stefan-lochbrunner/Pro-Trinket-USB-Keyboard/hw/Pro Trinket-Micro Keyboard Jr/hw/Pro Trinket-Micro Keyboard Jr v1.brd.png

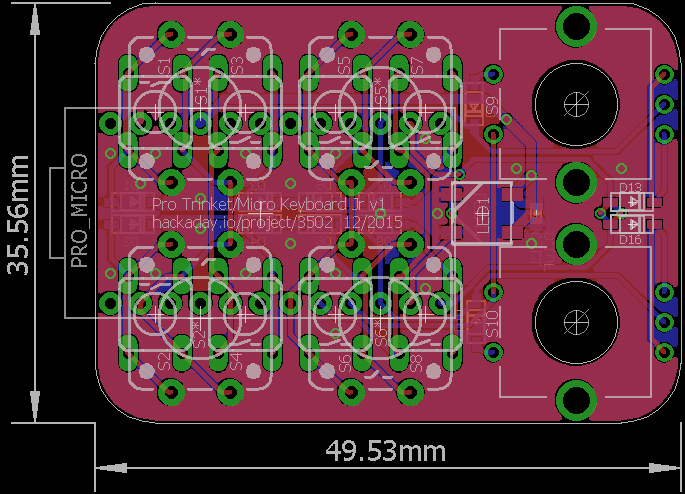
hw/Pro Trinket-Micro Keyboard Jr/hw/Pro Trinket-Micro Keyboard Jr v1.brd.png
