stefan-lochbrunner/Pro-Trinket-USB-Keyboard/Pro Trinket Keyboard/hw/schematics/Pro Trinket Keyboard V1.png

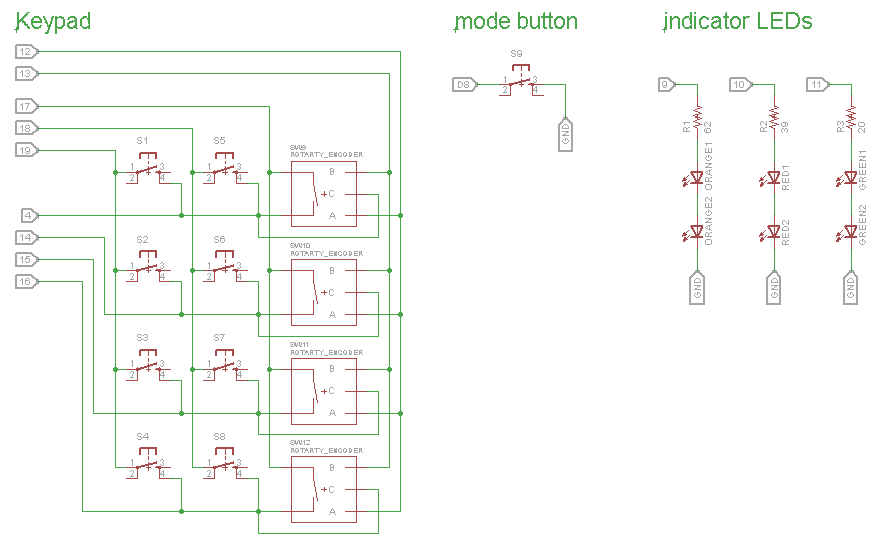
Pro Trinket Keyboard/hw/schematics/Pro Trinket Keyboard V1.png
