stefan-lochbrunner/Pro-Trinket-USB-Keyboard/Pro Trinket Keyboard/hw/schematics/Pro Trinket Keyboard V3.1.sch.png

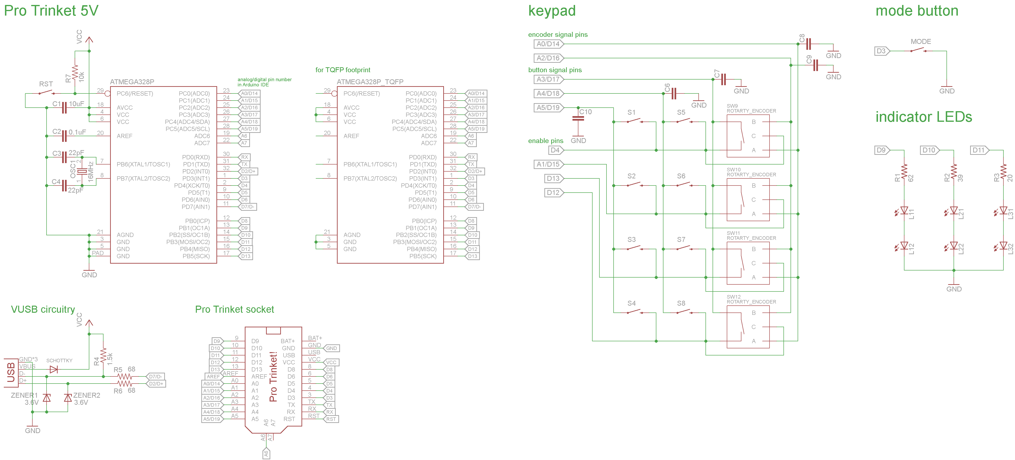
Pro Trinket Keyboard/hw/schematics/Pro Trinket Keyboard V3.1.sch.png
