stefan-lochbrunner/Pro-Trinket-USB-Keyboard/Pro Trinket Keyboard/hw/schematics/Pro Trinket Keyboard V3.3.brd.png

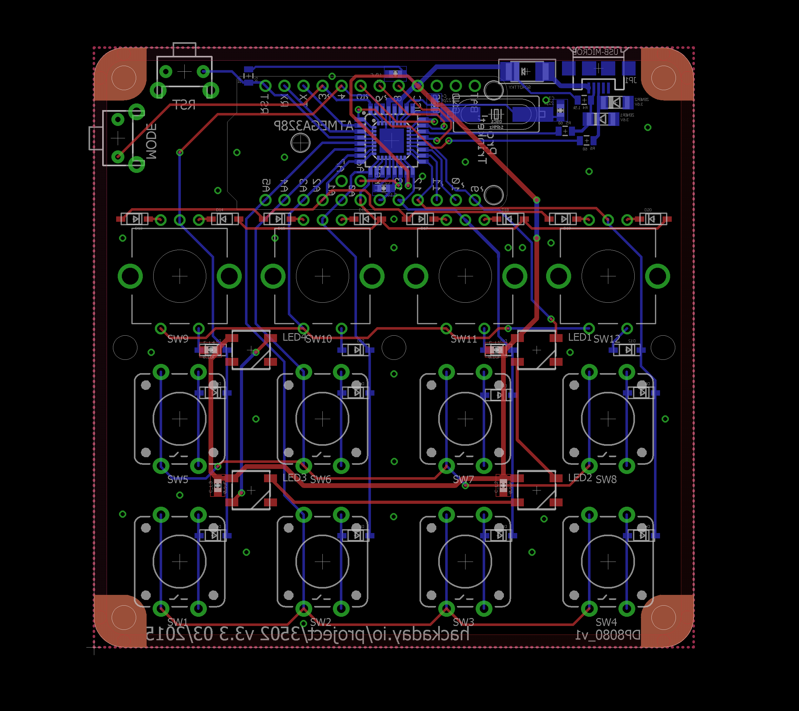
Pro Trinket Keyboard/hw/schematics/Pro Trinket Keyboard V3.3.brd.png
