stefan-lochbrunner/Pro-Trinket-USB-Keyboard/Pro Trinket Keyboard/hw/schematics/Pro Trinket Keyboard V4.2.brd.png

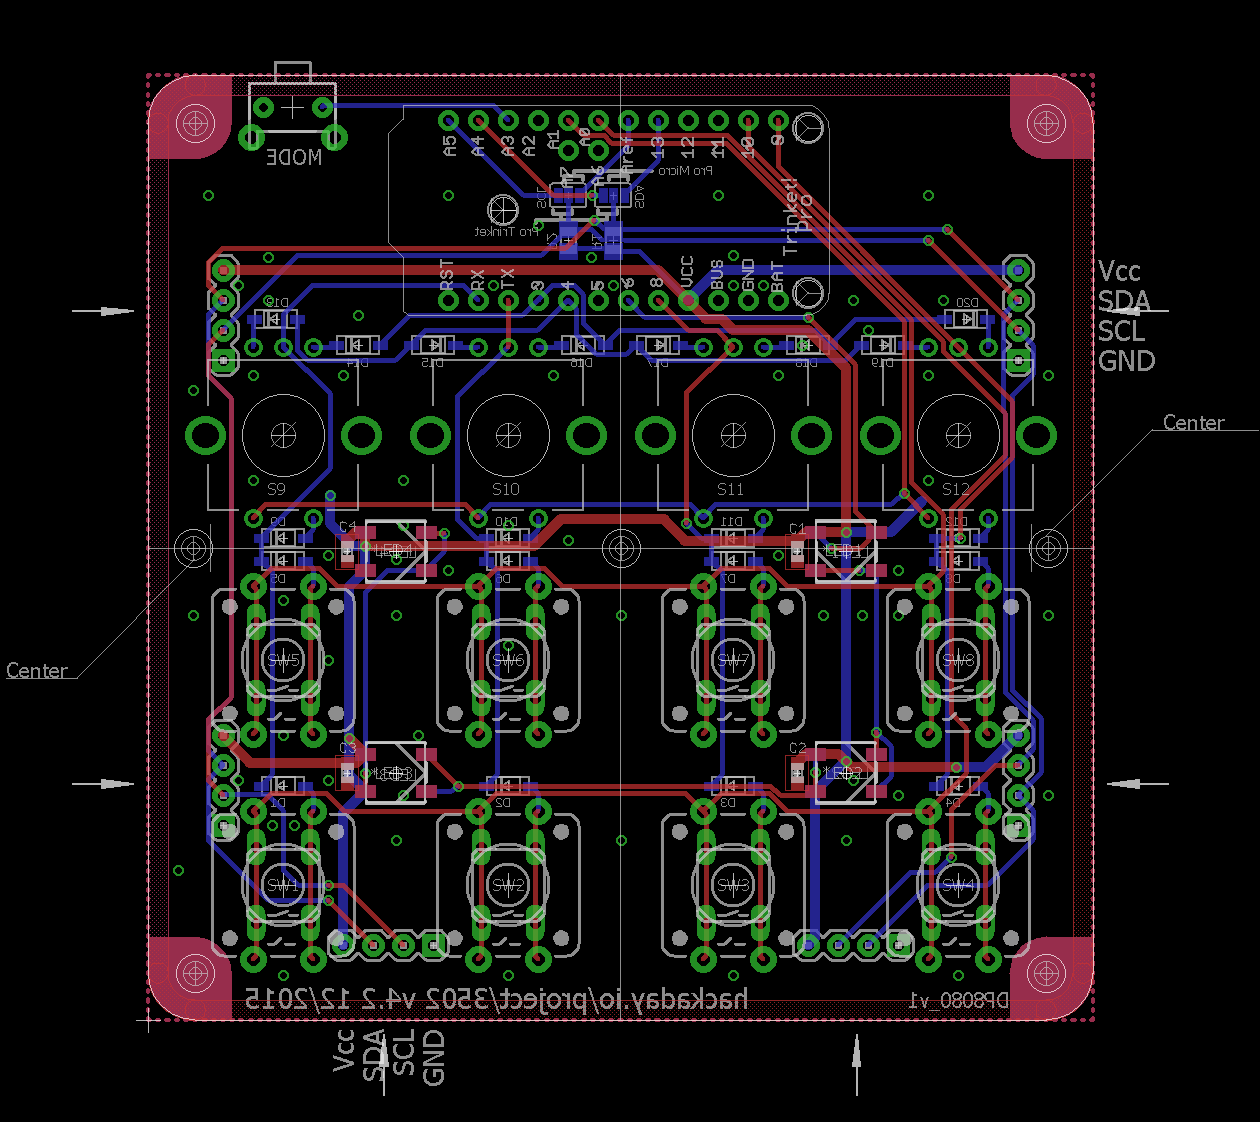
Pro Trinket Keyboard/hw/schematics/Pro Trinket Keyboard V4.2.brd.png
